davidcoulson/smart-tealight/hardware/flame-bulb/top.stl

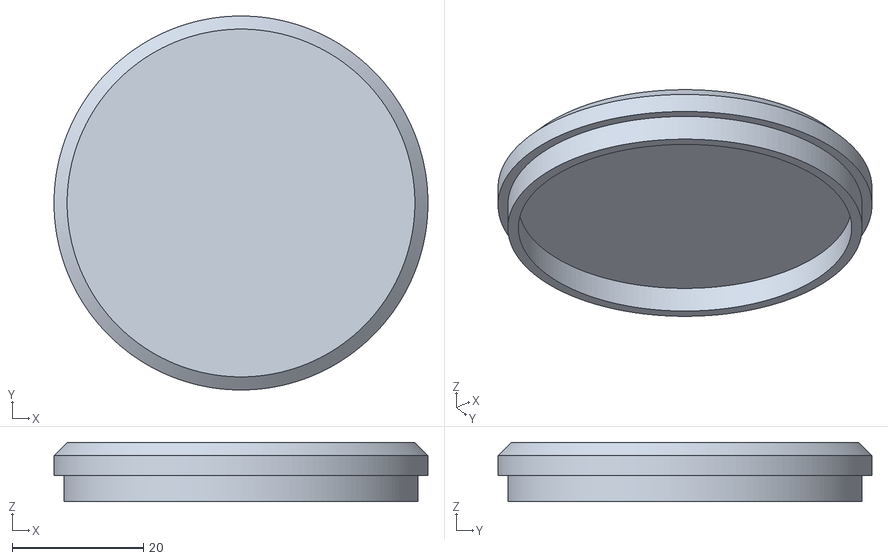
[picture p21: CAD file, 2026-09-27]
hardware/flame-bulb/top.stl
57.0 x 57.0 x 9.00
