davidcoulson/smart-tealight/hardware/flame-bulb/flame-bulb.3mf

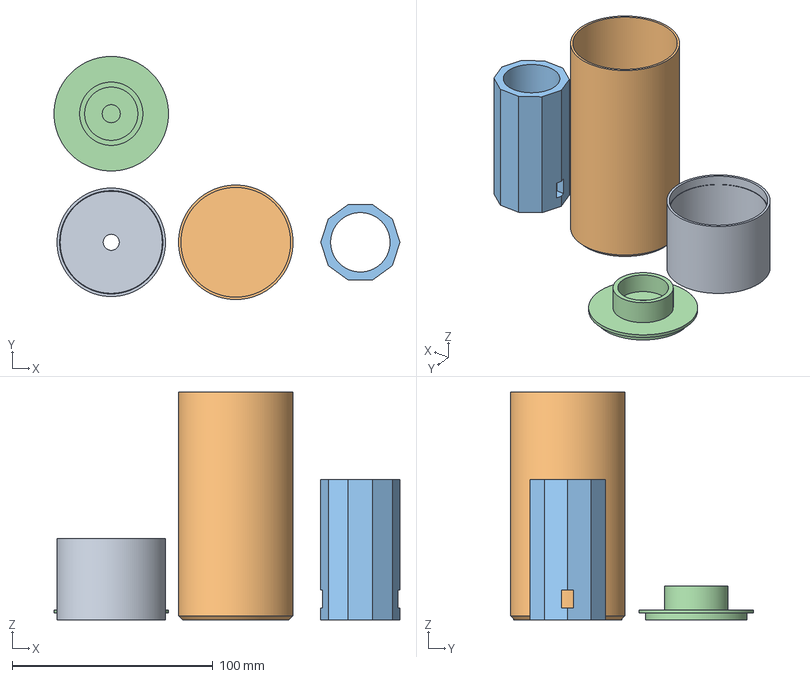
[picture p22: CAD file, 2026-09-27, an earlier design]
hardware/flame-bulb/flame-bulb.3mf
172.2 x 121.0 x 113.4 mm
base, inner (PC-FR, cavity up)
shade, full height (translucent, closed end DOWN)
core, 10 facets
cap + E26 plug cup (PC-FR)
