davidcoulson/smart-tealight/docs/ppk2-wiring.png

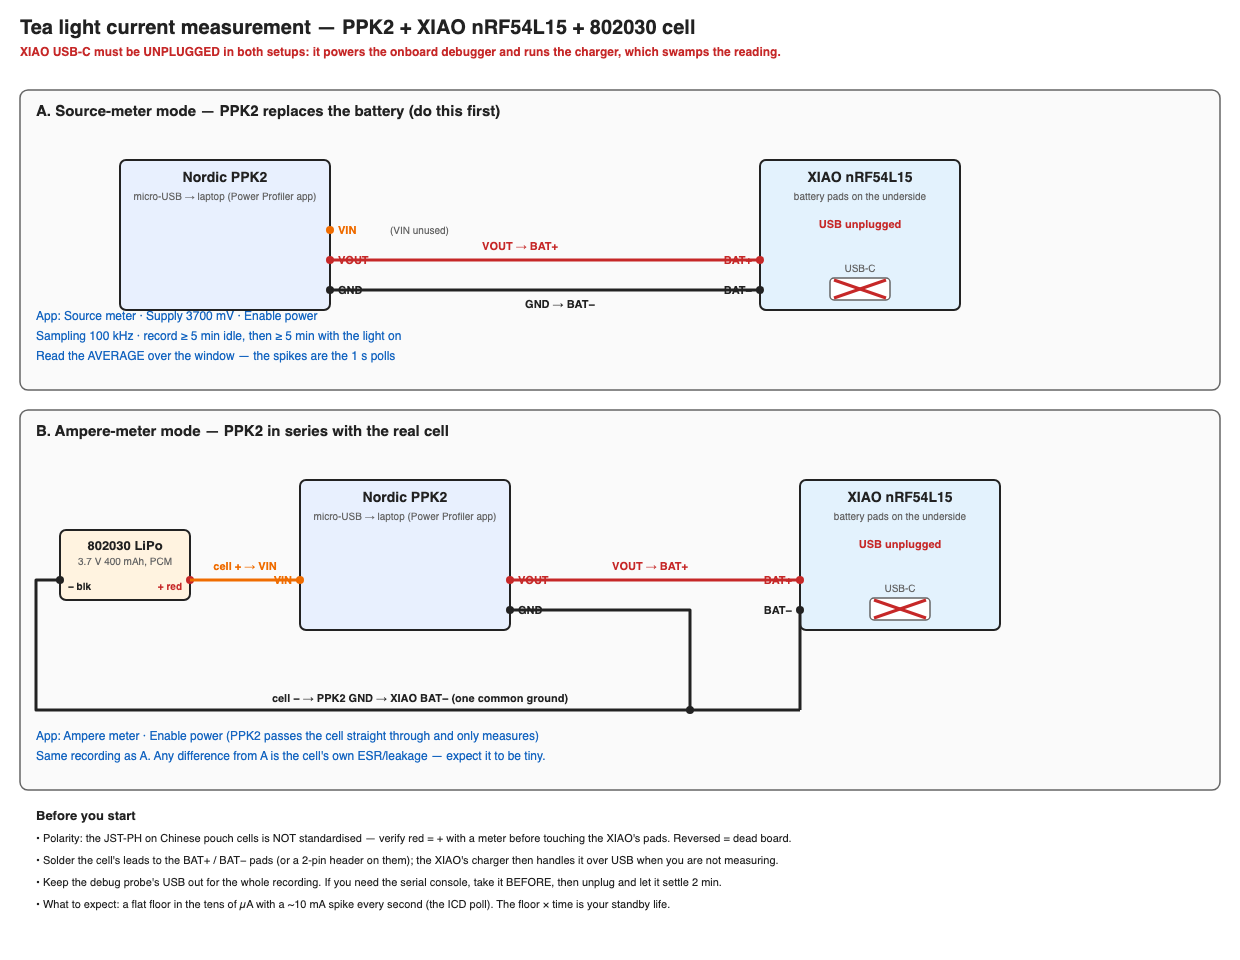
docs/ppk2-wiring.png
