davidcoulson/smart-tealight/hardware/flame-bulb/preview-assembled.png

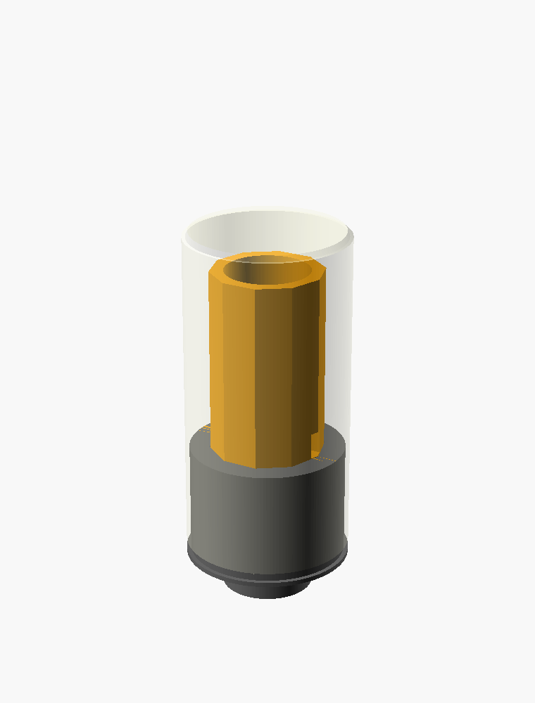
hardware/flame-bulb/preview-assembled.png
