davidcoulson/smart-tealight/hardware/flame-bulb/preview-v2-assembled.png

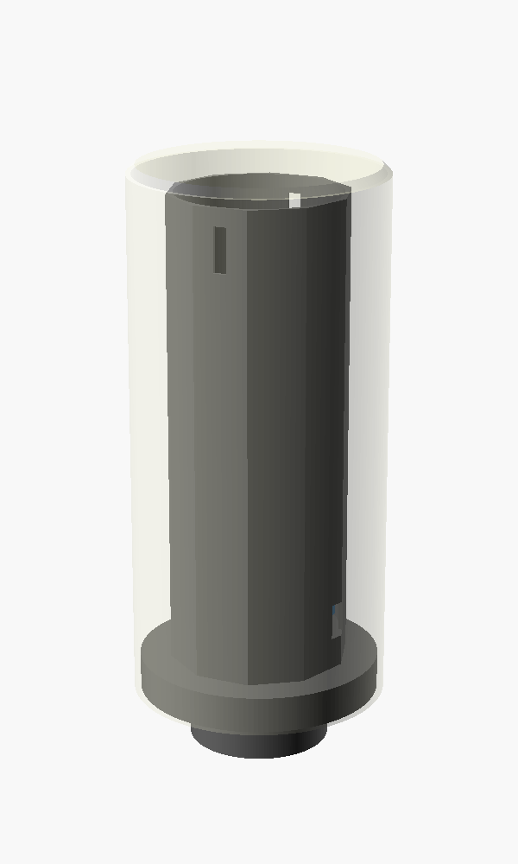
hardware/flame-bulb/preview-v2-assembled.png
